Jonastjep/CRAPy/docs/assets/images/2-axis-ultrasound-mount-alternative-2020-jun-22-03-10-50pm-000-customizedview364675981-png-1172x879.png

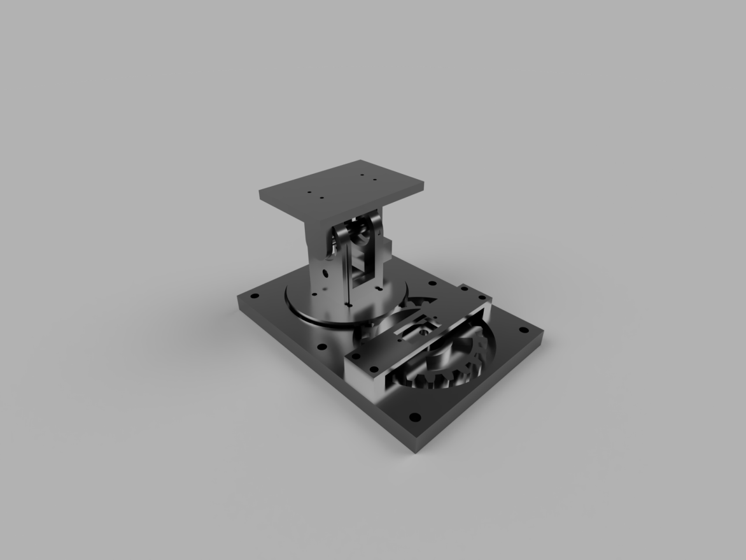
docs/assets/images/2-axis-ultrasound-mount-alternative-2020-jun-22-03-10-50pm-000-customizedview364675981-png-1172x879.png
