Jonastjep/CRAPy/docs/assets/images/71f26799-833d-4c4f-81e4-07bcf592b78a-1600x1200-800x600.jpg

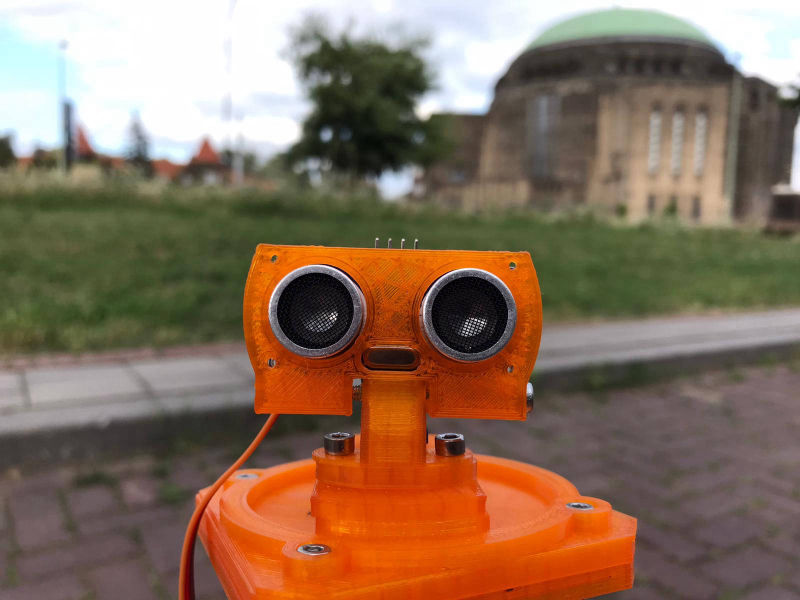
docs/assets/images/71f26799-833d-4c4f-81e4-07bcf592b78a-1600x1200-800x600.jpg
