Jonastjep/CRAPy/docs/assets/images/57156695-2302990599990614-2368464688951328768-n-510x510.jpg

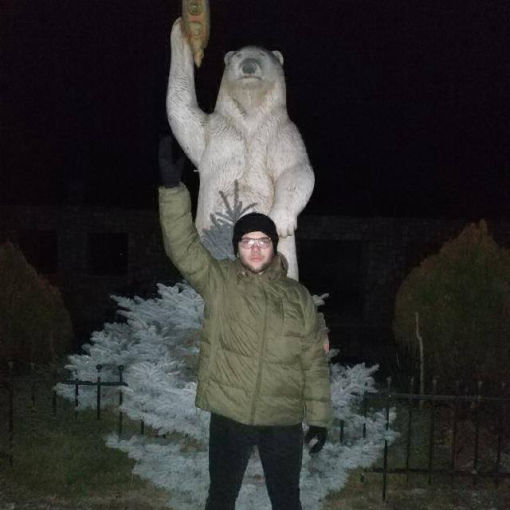
docs/assets/images/57156695-2302990599990614-2368464688951328768-n-510x510.jpg
