Jonastjep/CRAPy/docs/assets/images/73093326-130693628344035-692487221779874885-n-510x510.jpg

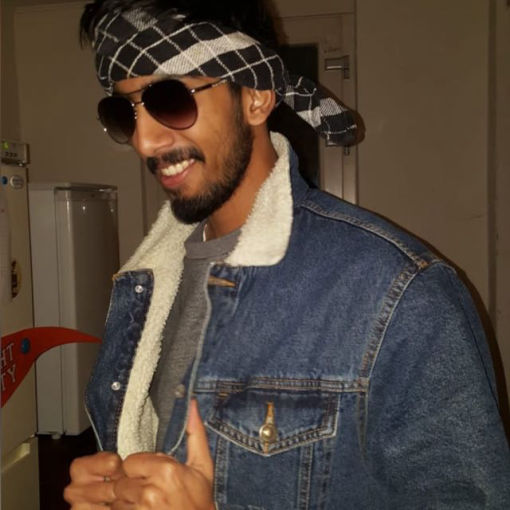
docs/assets/images/73093326-130693628344035-692487221779874885-n-510x510.jpg
