Jonastjep/CRAPy/docs/assets/images/dirt-render-1-2000x1500.png

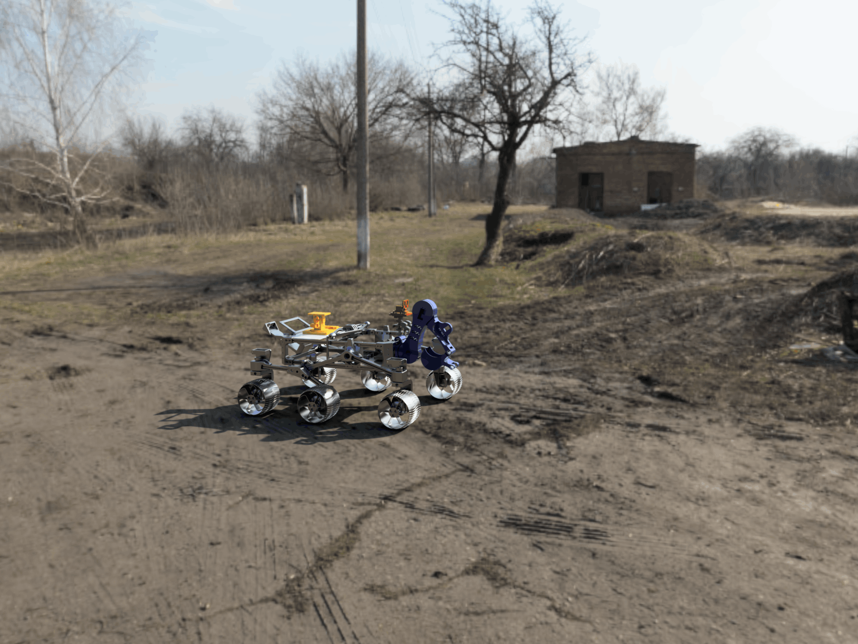
docs/assets/images/dirt-render-1-2000x1500.png
