Jonastjep/CRAPy/docs/assets/images/field-render-2-2000x1500.png

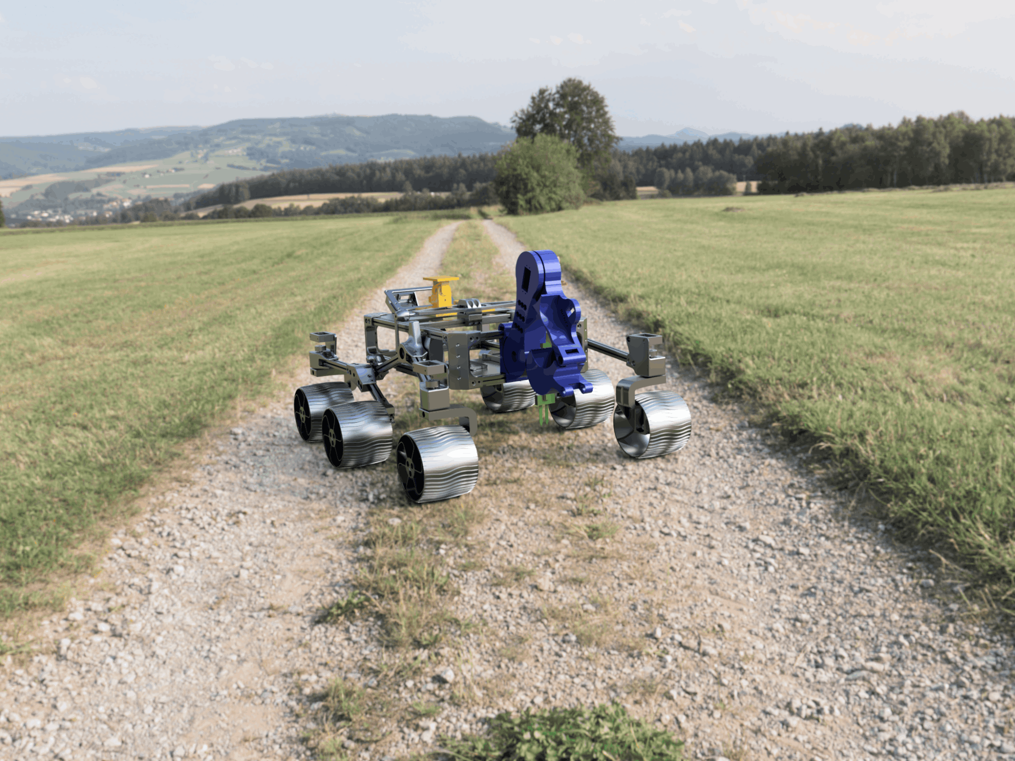
docs/assets/images/field-render-2-2000x1500.png
