Jonastjep/CRAPy/docs/assets/images/grey-render-1-2000x1500.png

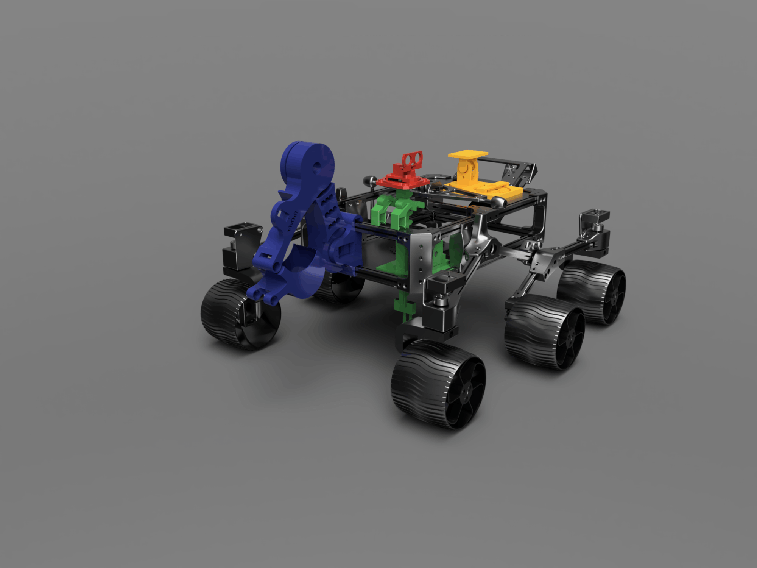
docs/assets/images/grey-render-1-2000x1500.png
