Jonastjep/CRAPy/docs/assets/images/lake-bed-render-1-2000x1500.png

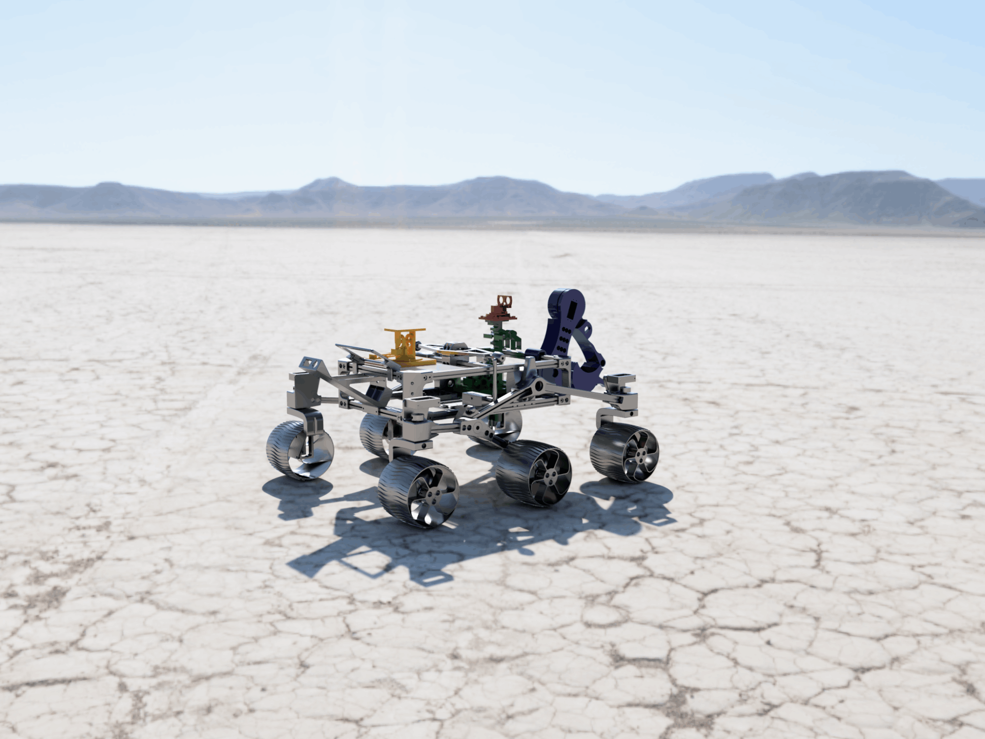
docs/assets/images/lake-bed-render-1-2000x1500.png
