Jonastjep/CRAPy/docs/assets/images/mobirise2020529-131212020-5-2-9-52-14.jpg

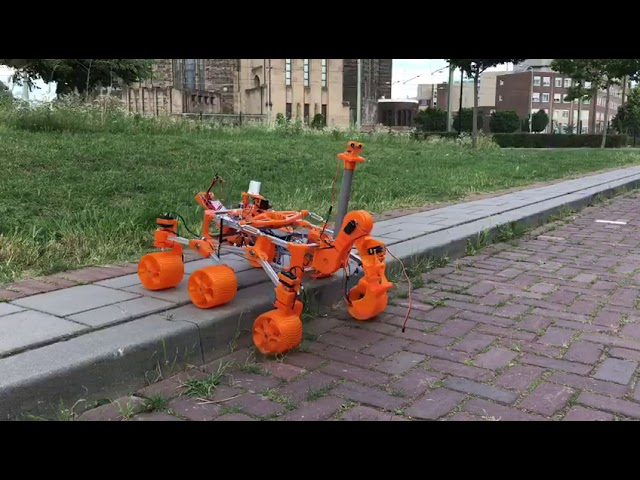
docs/assets/images/mobirise2020529-131212020-5-2-9-52-14.jpg
