Jonastjep/CRAPy/docs/assets/images/radar-humidity-sensor-with-corrected-gear-2020-jun-22-03-23-32pm-000-customizedview1042665837-png-760x570.png

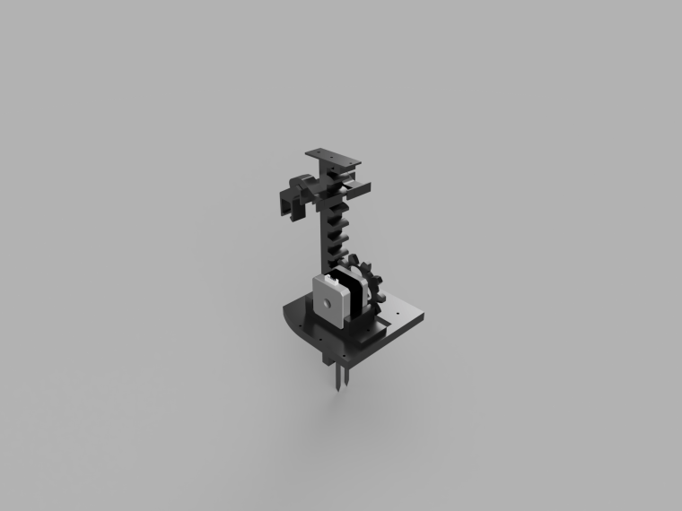
docs/assets/images/radar-humidity-sensor-with-corrected-gear-2020-jun-22-03-23-32pm-000-customizedview1042665837-png-760x570.png
