Jonastjep/CRAPy/docs/assets/images/screen-shot-2020-06-22-at-6.25.10-pm-510x510.png

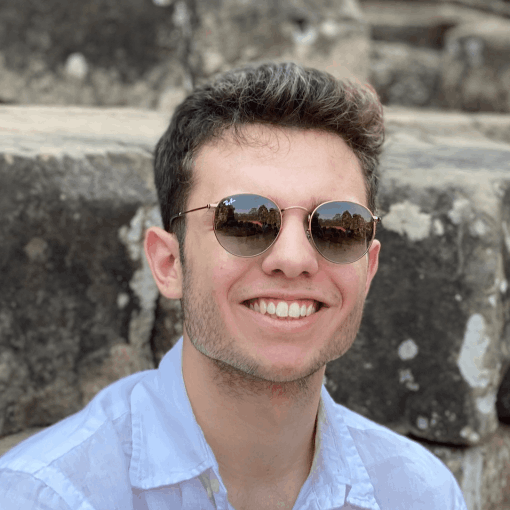
docs/assets/images/screen-shot-2020-06-22-at-6.25.10-pm-510x510.png
