Jonastjep/CRAPy/docs/assets/images/screen-shot-2020-06-23-at-1.39.27-pm-510x510.png

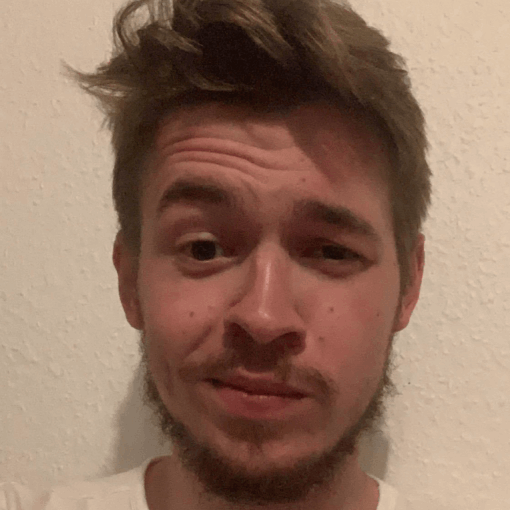
docs/assets/images/screen-shot-2020-06-23-at-1.39.27-pm-510x510.png
