Jonastjep/CRAPy/docs/assets/images/screen-shot-2020-06-26-at-7.56.01-pm-510x510.png

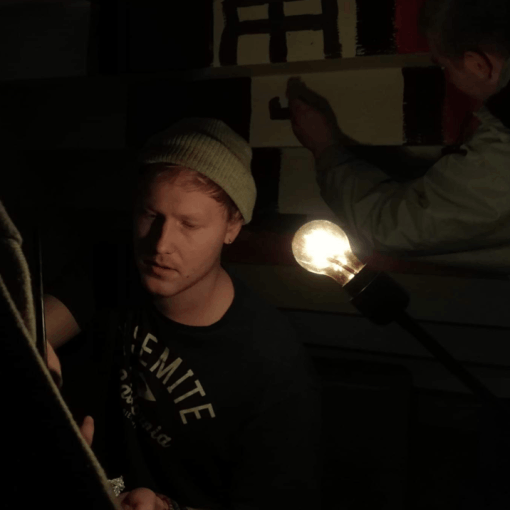
docs/assets/images/screen-shot-2020-06-26-at-7.56.01-pm-510x510.png
