Jonastjep/CRAPy/docs/assets/images/screen-shot-2020-06-26-at-7.56.23-pm-496x496.png

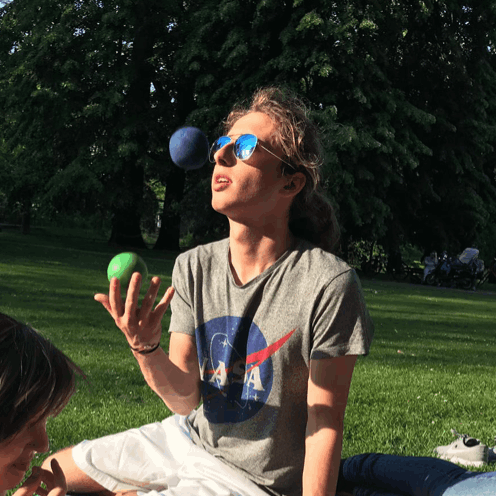
docs/assets/images/screen-shot-2020-06-26-at-7.56.23-pm-496x496.png
