Jonastjep/CRAPy/docs/assets/images/screen-shot-2020-06-26-at-8.29.14-pm-510x508.png

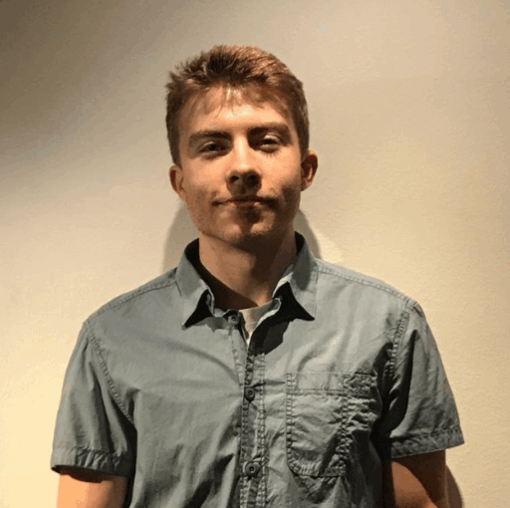
docs/assets/images/screen-shot-2020-06-26-at-8.29.14-pm-510x508.png
