Jonastjep/CRAPy/docs/assets/images/screen-shot-2020-06-26-at-10.00.35-pm-504x504.png

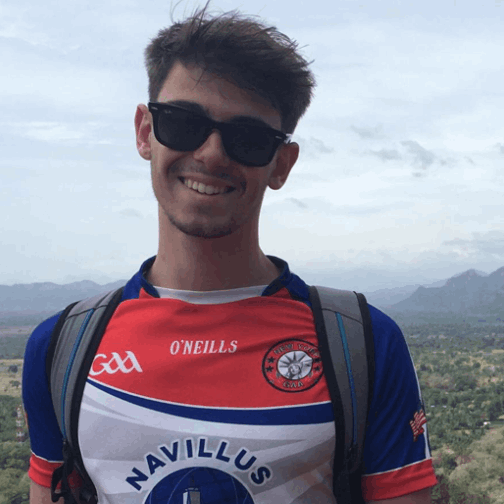
docs/assets/images/screen-shot-2020-06-26-at-10.00.35-pm-504x504.png
