Jonastjep/CRAPy/docs/assets/images/screen-shot-2020-06-30-at-11.55.34-am-1776x966.png

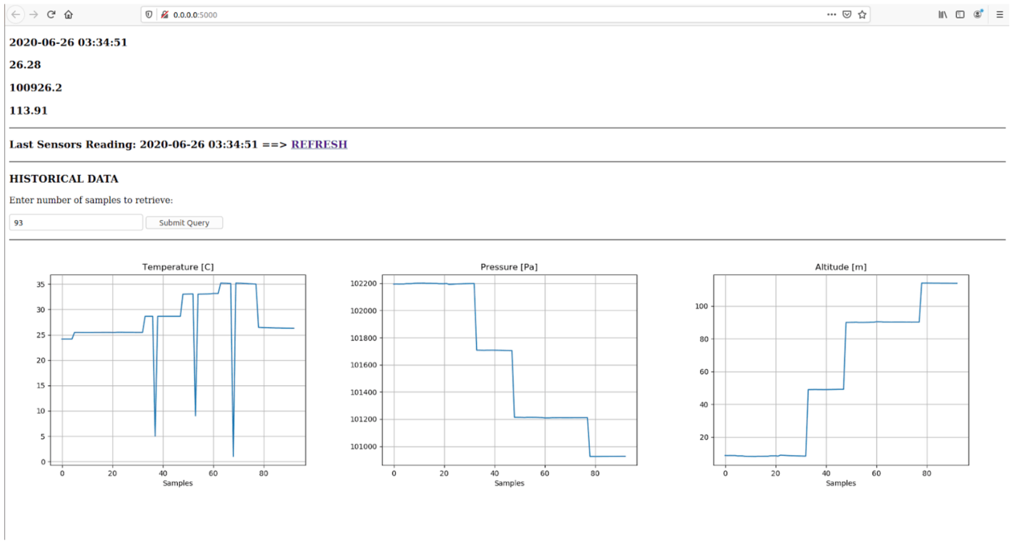
docs/assets/images/screen-shot-2020-06-30-at-11.55.34-am-1776x966.png
