Jonastjep/CRAPy/docs/assets/images/screen-shot-2020-06-30-at-12.00.35-pm-1398x910.png

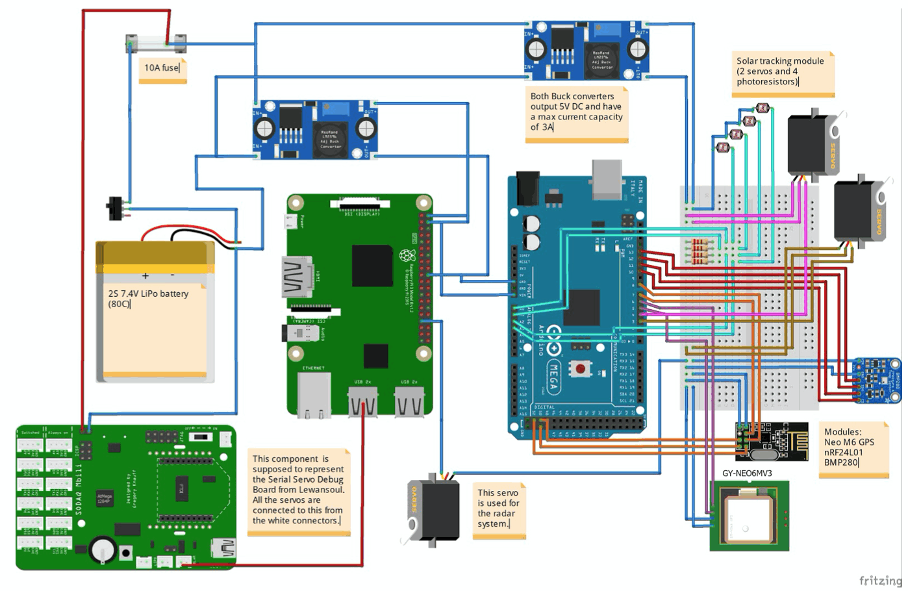
docs/assets/images/screen-shot-2020-06-30-at-12.00.35-pm-1398x910.png
