Jonastjep/CRAPy/docs/assets/images/screen-shot-2020-06-30-at-12.02.44-pm-1000x487.png

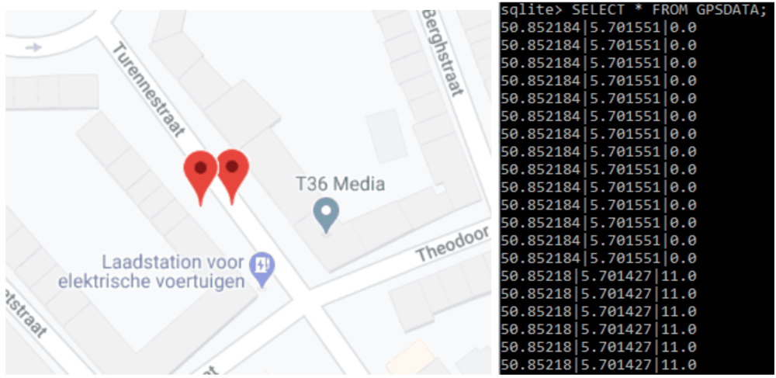
docs/assets/images/screen-shot-2020-06-30-at-12.02.44-pm-1000x487.png
