Jonastjep/CRAPy/docs/assets/images/single-axis-mount-2020-jun-22-03-18-49pm-000-customizedview30529642915-png-760x570.png

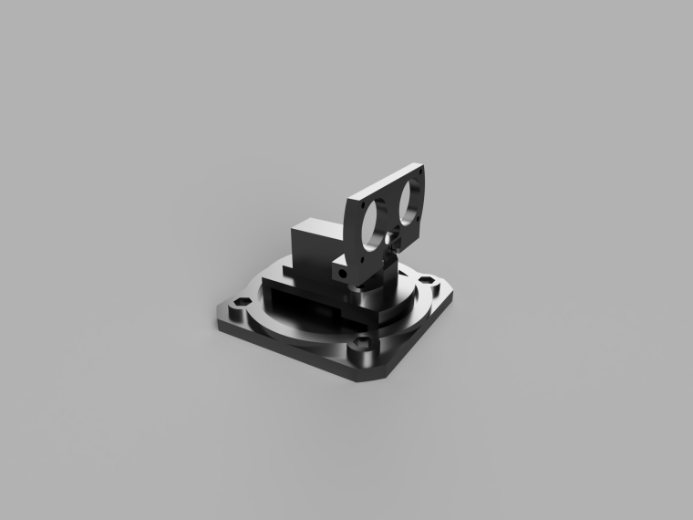
docs/assets/images/single-axis-mount-2020-jun-22-03-18-49pm-000-customizedview30529642915-png-760x570.png
