Jonastjep/CRAPy/docs/assets/images/whatsapp-image-2020-06-18-at-18.16.16-2000x1125-800x450.jpg

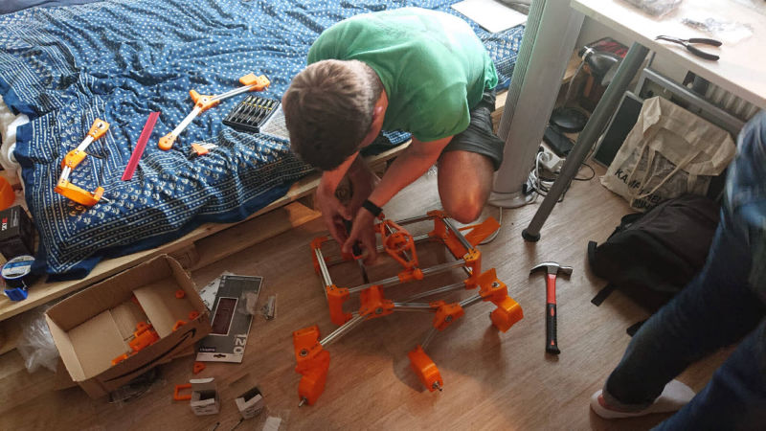
docs/assets/images/whatsapp-image-2020-06-18-at-18.16.16-2000x1125-800x450.jpg
