Jonastjep/CRAPy/docs/assets/images/white-render-1-copy-2048x1266.png

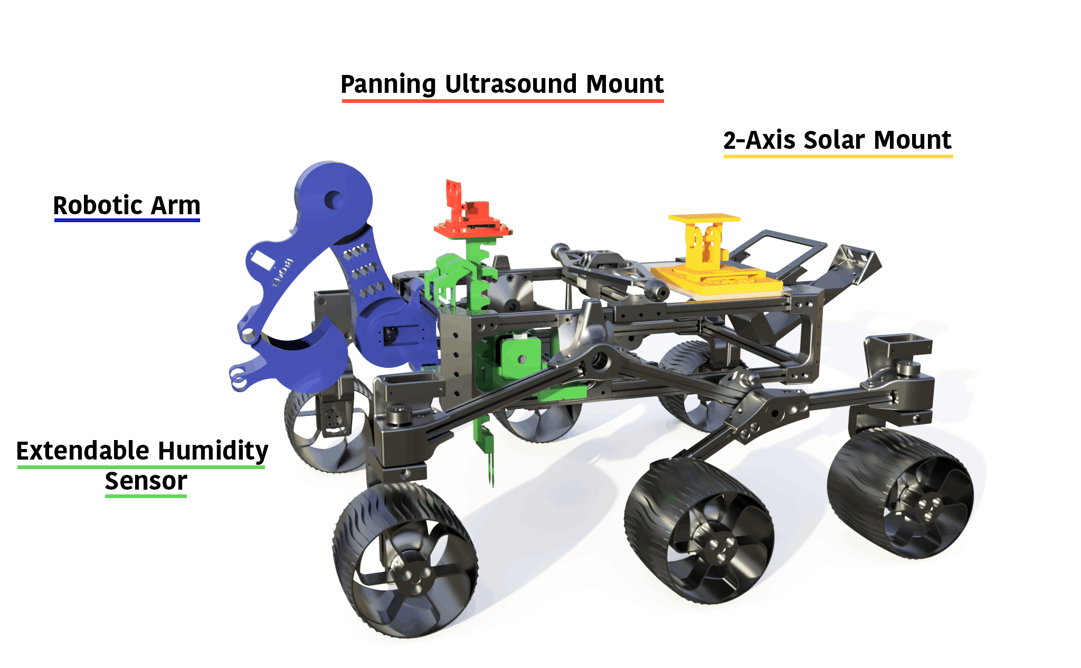
docs/assets/images/white-render-1-copy-2048x1266.png
