Jonastjep/CRAPy/docs/assets/images/ydxj0181-2530x1304.jpg

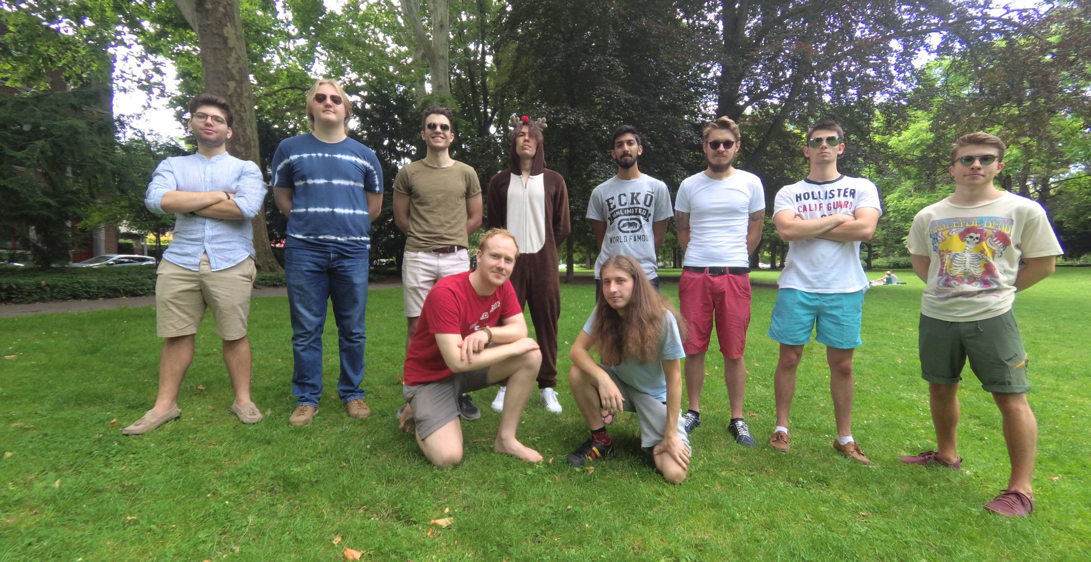
docs/assets/images/ydxj0181-2530x1304.jpg
