Jonastjep/CRAPy/3d Files/Sensor Mast v22 indv comp/Backing Shield.stl

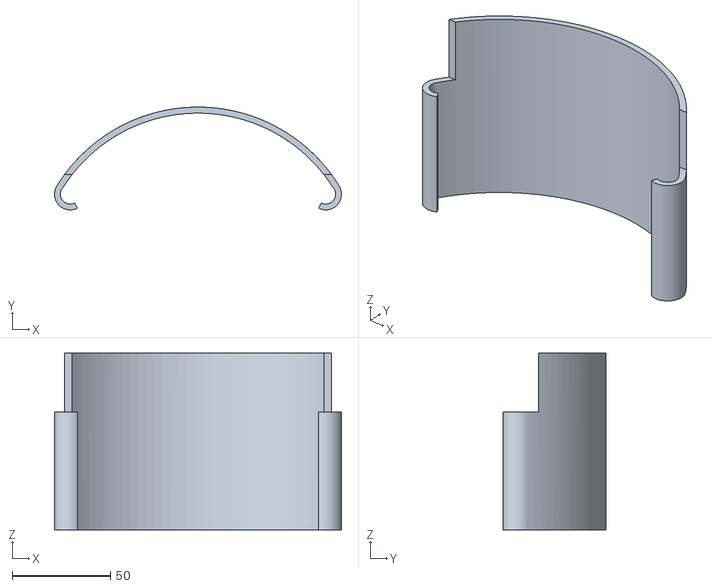
[picture p47: CAD file, 2021-01-25]
3d Files/Sensor Mast v22 indv comp/Backing Shield.stl
146.0 x 52.3 x 90.0
