Jonastjep/CRAPy/docs/assets/images/assembly-2020-jun-22-03-05-00pm-000-customizedview20428002416-png-1172x879.png

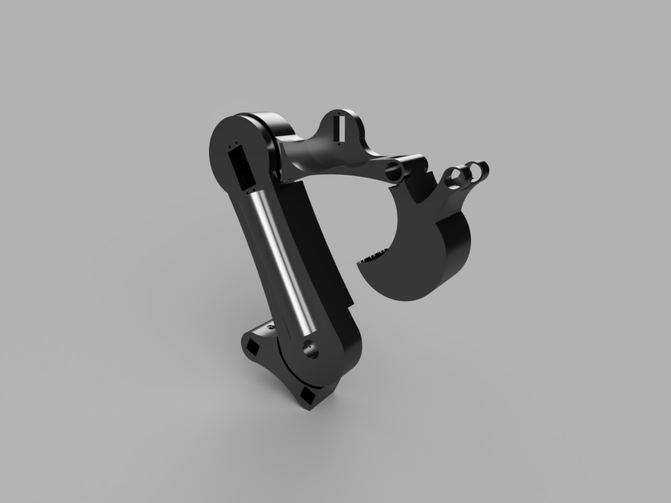
docs/assets/images/assembly-2020-jun-22-03-05-00pm-000-customizedview20428002416-png-1172x879.png
